Animal-Crate/Animal-Crate/Building Resources/CAD Designs/Animals/Dog/dog.stl

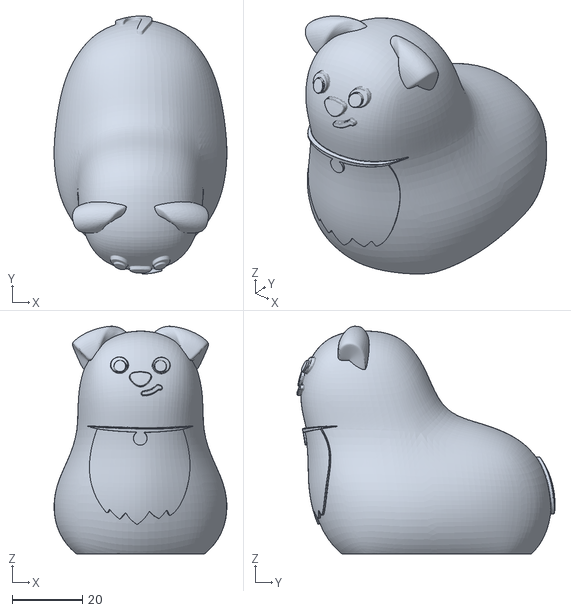
[picture p26: CAD file, 2025-05-05]
Building Resources/CAD Designs/Animals/Dog/dog.stl
49.1 x 73.4 x 64.7
