Animal-Crate/Animal-Crate/Building Resources/CAD Designs/Animals/inside panel.stl

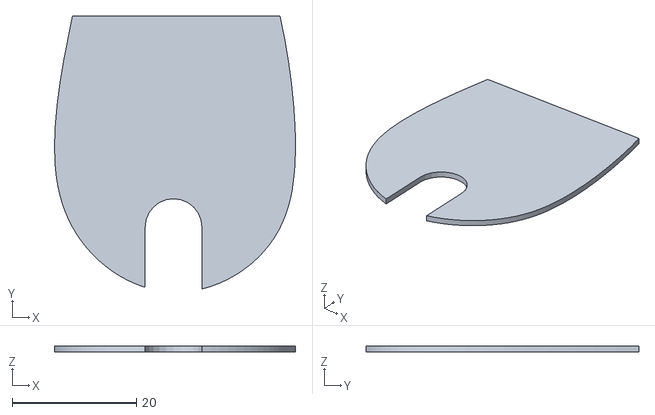
[picture p27: CAD file, 2025-05-05]
Building Resources/CAD Designs/Animals/inside panel.stl
38.8 x 43.9 x 1.02
