Animal-Crate/Animal-Crate/Building Resources/CAD Designs/Animals/Pig/pig color.3mf

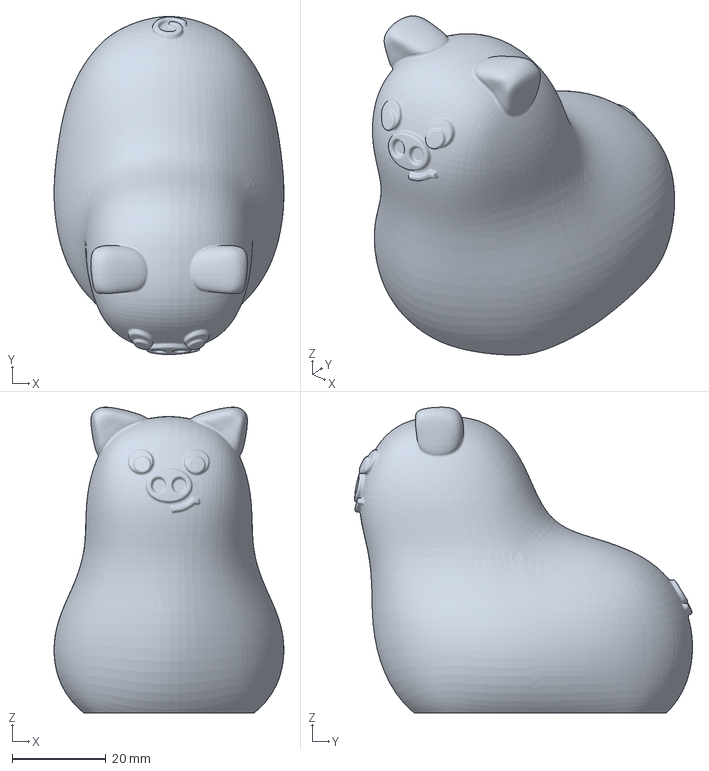
[picture p28: CAD file, 2025-05-05]
Building Resources/CAD Designs/Animals/Pig/pig color.3mf
49.1 x 72.3 x 65.4 mm
