Animal-Crate/Animal-Crate/Building Resources/CAD Designs/Barn/Body/Barn Body Back.STL

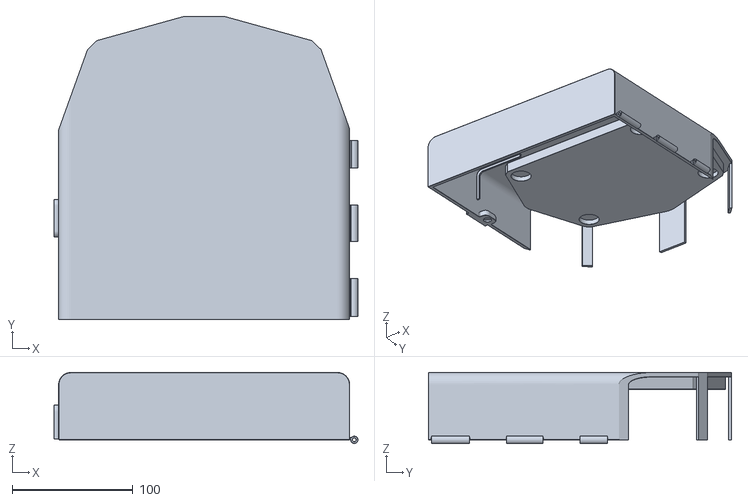
[picture p29: CAD file, 2025-05-05]
Building Resources/CAD Designs/Barn/Body/Barn Body Back.STL
252.0 x 251.5 x 58.9
