Animal-Crate/Animal-Crate/Building Resources/CAD Designs/Barn/Shelves/EEBarn5shelf2.STL

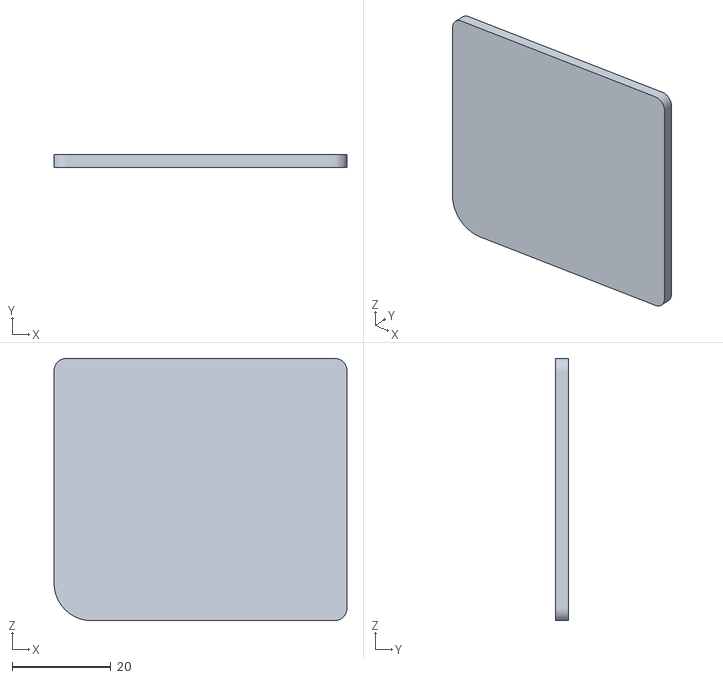
[picture p30: CAD file, 2025-05-05]
Building Resources/CAD Designs/Barn/Shelves/EEBarn5shelf2.STL
59.4 x 2.54 x 53.2
