Animal-Crate/Animal-Crate/Building Resources/CAD Designs/Barn/Small Parts/window frame.STL

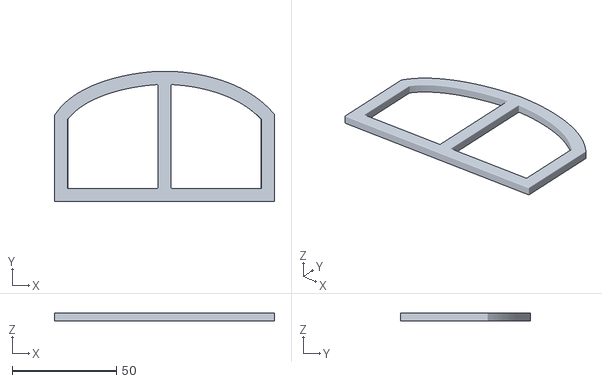
[picture p31: CAD file, 2025-05-05]
Building Resources/CAD Designs/Barn/Small Parts/window frame.STL
105.4 x 62.4 x 3.81
