Animal-Crate/Animal-Crate/Building Resources/CAD Designs/Tablet/Fence Pieces/fence hole1.STL

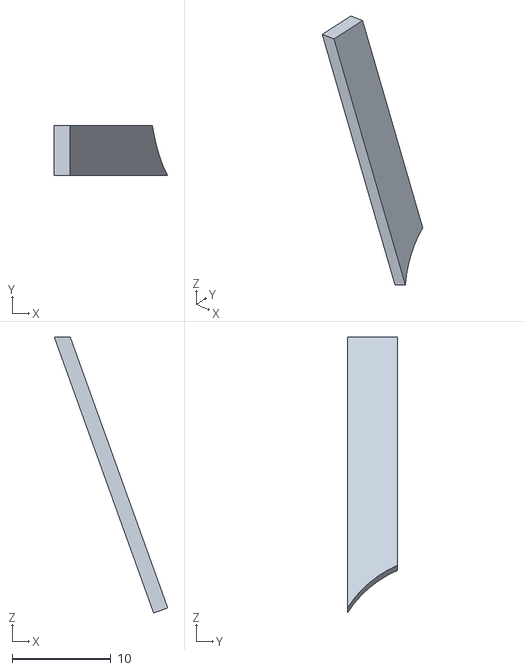
[picture p32: CAD file, 2025-05-05]
Building Resources/CAD Designs/Tablet/Fence Pieces/fence hole1.STL
11.5 x 5.08 x 28.0
