Animal-Crate/Animal-Crate/Building Resources/CAD Designs/Tablet/tablet battery panel.STL

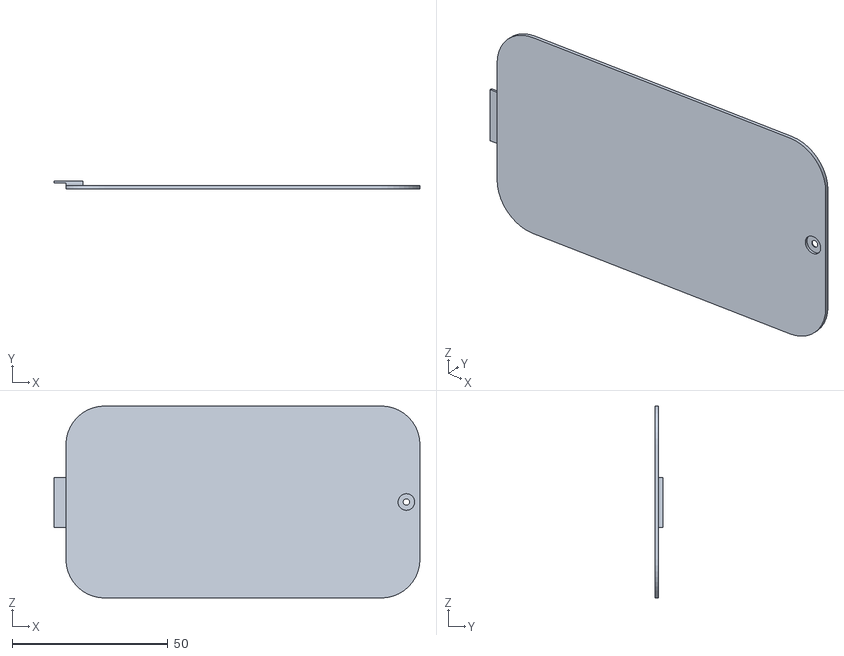
[picture p33: CAD file, 2025-05-05]
Building Resources/CAD Designs/Tablet/tablet battery panel.STL
117.6 x 2.41 x 61.7
