Animal-Crate/Animal-Crate/Building Resources/CAD Designs/Barn/Small Parts/hinge cap.STL

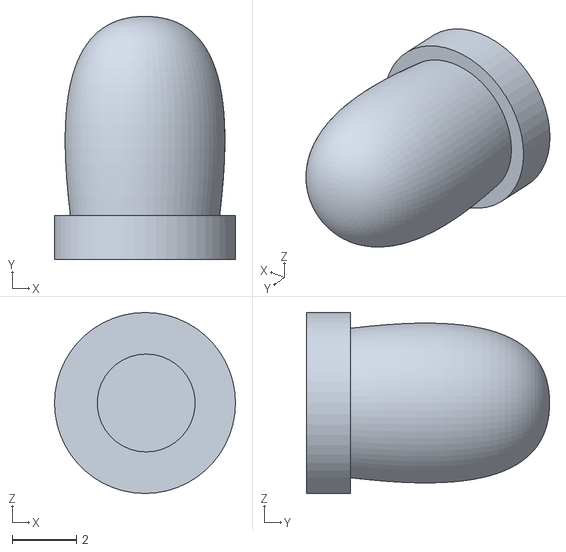
[picture p34: CAD file, 2025-05-05]
Building Resources/CAD Designs/Barn/Small Parts/hinge cap.STL
5.64 x 7.58 x 5.64
