Animal-Crate/Animal-Crate/Building Resources/CAD Designs/Tablet/Fence Pieces/fence 2 hole 3.STL

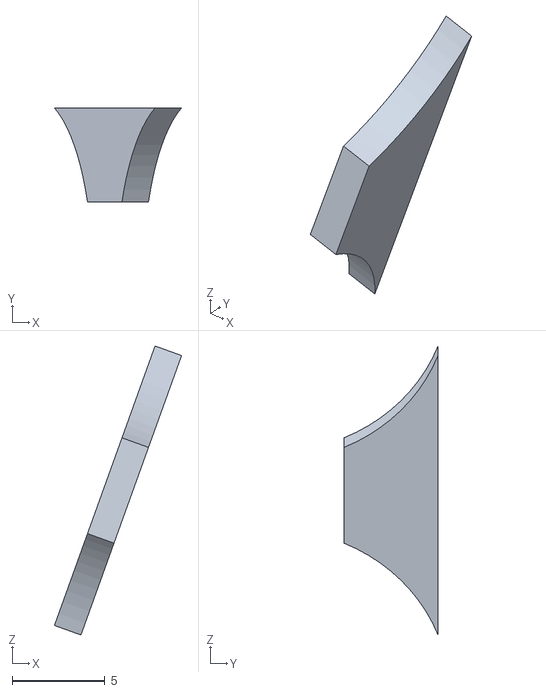
[picture p35: CAD file, 2025-05-05]
Building Resources/CAD Designs/Tablet/Fence Pieces/fence 2 hole 3.STL
6.87 x 5.08 x 15.6
