Animal-Crate/Animal-Crate/Building Resources/CAD Designs/Tablet/tablet back panel.STL

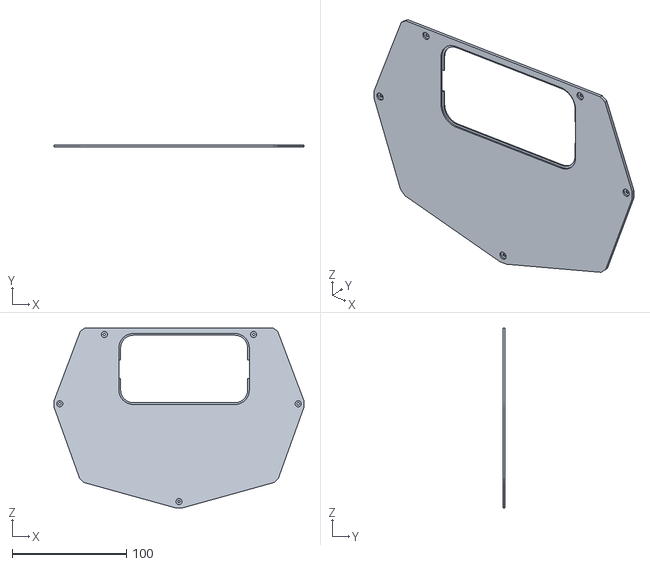
[picture p36: CAD file, 2025-05-05]
Building Resources/CAD Designs/Tablet/tablet back panel.STL
219.1 x 2.03 x 157.6
