Animal-Crate/Animal-Crate/Building Resources/CAD Designs/Barn/Shelves/EEBarn5shelf1.STL

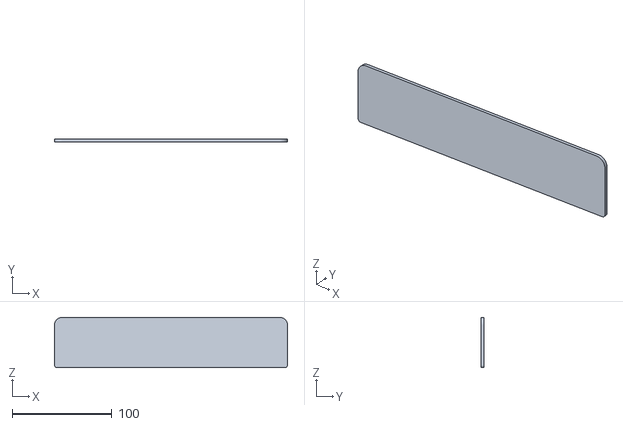
[picture p37: CAD file, 2025-05-05]
Building Resources/CAD Designs/Barn/Shelves/EEBarn5shelf1.STL
233.2 x 2.54 x 50.3
