Animal-Crate/Animal-Crate/Building Resources/CAD Designs/Tablet/Fence Pieces/fence hole 3.STL

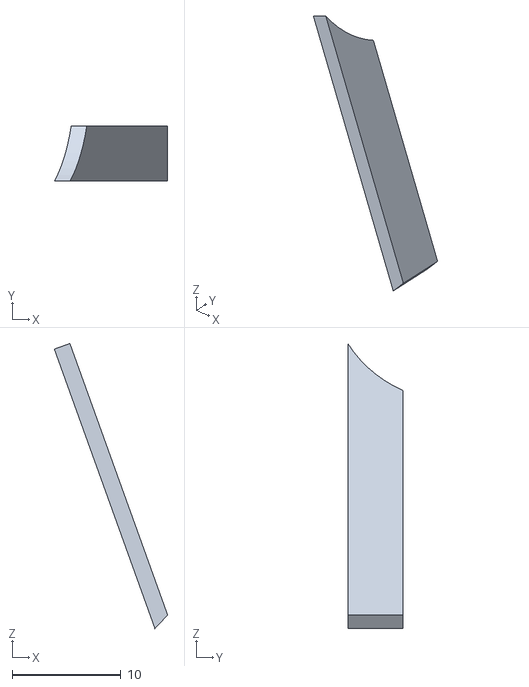
[picture p38: CAD file, 2025-05-05]
Building Resources/CAD Designs/Tablet/Fence Pieces/fence hole 3.STL
10.4 x 5.08 x 26.2
