Animal-Crate/Animal-Crate/Building Resources/CAD Designs/Tablet/tablet model.STEP

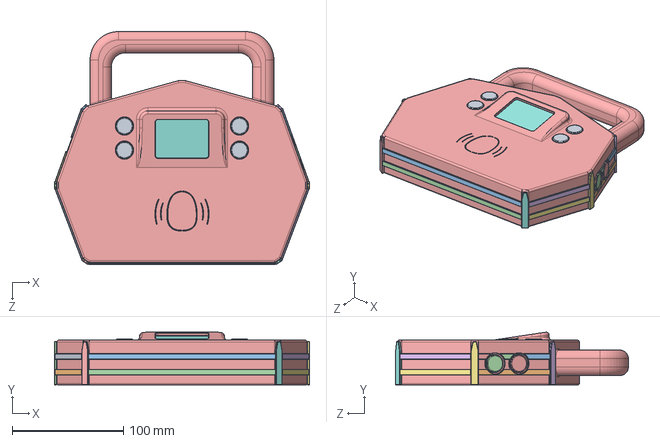
[picture p39: CAD file, 2025-05-05]
Building Resources/CAD Designs/Tablet/tablet model.STEP
228.9 x 47.3 x 209.0 mm
