Animal-Crate/Animal-Crate/Building Resources/CAD Designs/Tablet/Fence Pieces/fence hole 4.STL

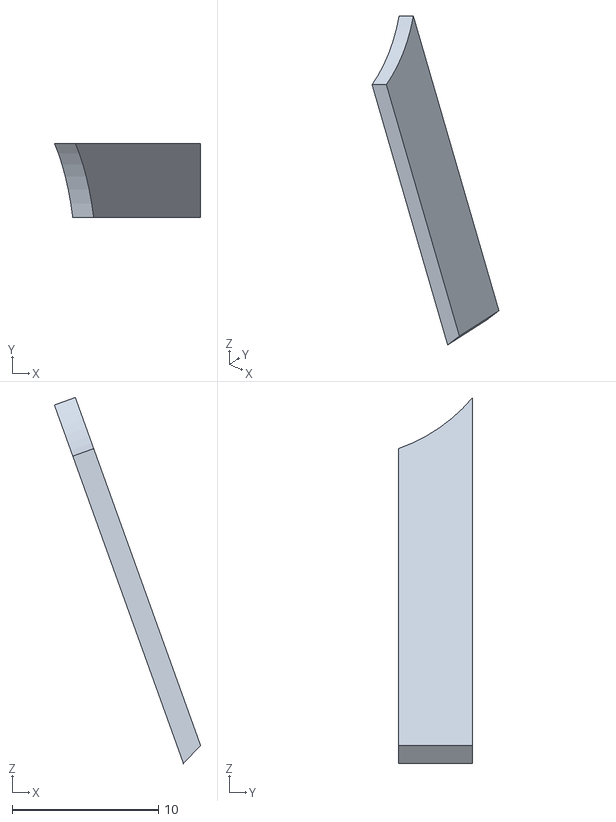
[picture p40: CAD file, 2025-05-05]
Building Resources/CAD Designs/Tablet/Fence Pieces/fence hole 4.STL
10.0 x 5.08 x 25.1
