Animal-Crate/Animal-Crate/Building Resources/CAD Designs/Tablet/Fence Pieces/fence long.STL

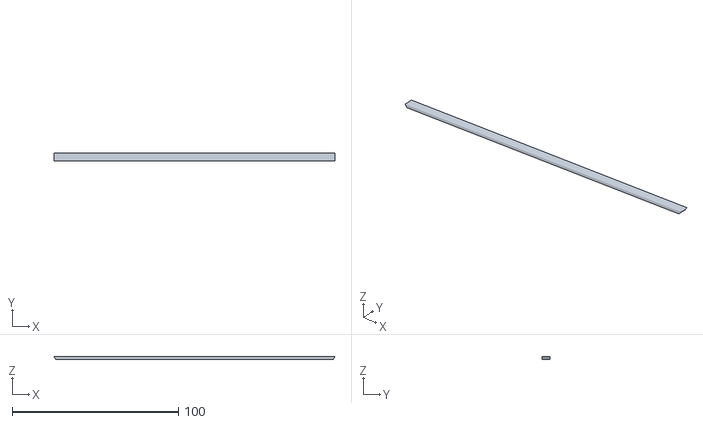
[picture p41: CAD file, 2025-05-05]
Building Resources/CAD Designs/Tablet/Fence Pieces/fence long.STL
168.8 x 5.08 x 1.52
