Animal-Crate/Animal-Crate/Building Resources/CAD Designs/Tablet/Fence Pieces/fence 2 hole 4.STL

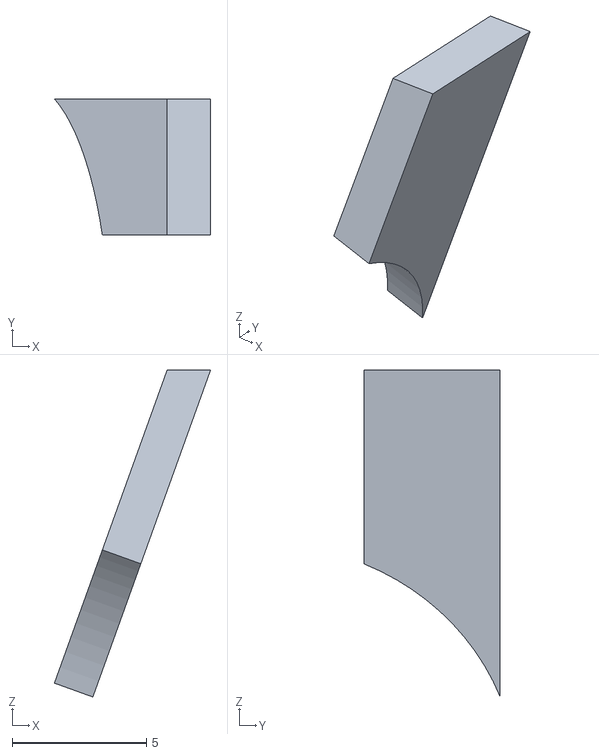
[picture p42: CAD file, 2025-05-05]
Building Resources/CAD Designs/Tablet/Fence Pieces/fence 2 hole 4.STL
5.82 x 5.08 x 12.2
