Animal-Crate/Animal-Crate/Building Resources/CAD Designs/Tablet/Fence Pieces/fence 1.STL

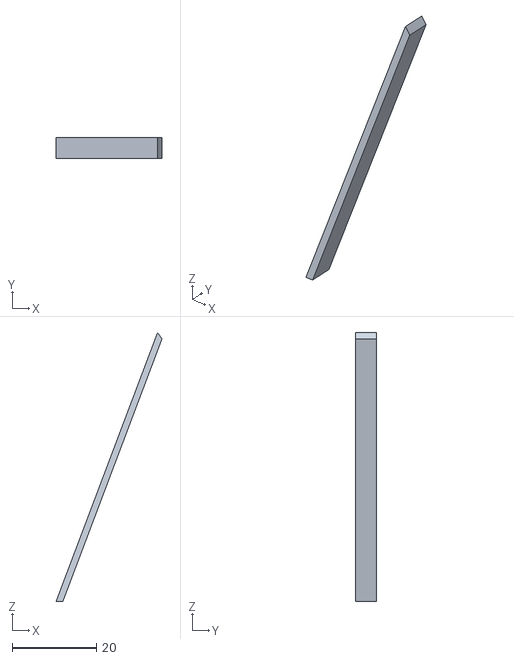
[picture p43: CAD file, 2025-05-05]
Building Resources/CAD Designs/Tablet/Fence Pieces/fence 1.STL
25.2 x 5.08 x 63.9
