Animal-Crate/Animal-Crate/Building Resources/CAD Designs/Tablet/Fence Pieces/fence hole 2.STL

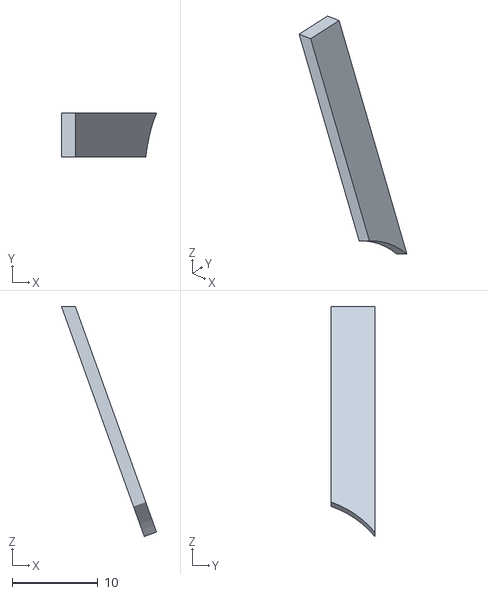
[picture p44: CAD file, 2025-05-05]
Building Resources/CAD Designs/Tablet/Fence Pieces/fence hole 2.STL
11.1 x 5.08 x 26.8
