Animal-Crate/Animal-Crate/Building Resources/CAD Designs/Tablet/Fence Pieces/fence 2 hole 1.STL

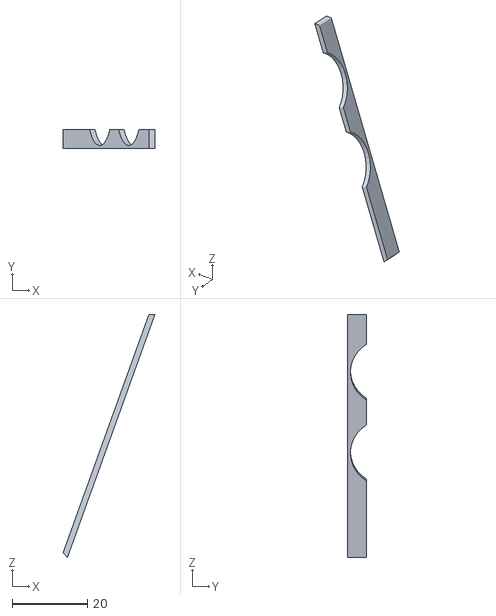
[picture p45: CAD file, 2025-05-05]
Building Resources/CAD Designs/Tablet/Fence Pieces/fence 2 hole 1.STL
24.5 x 5.08 x 64.7
